mean00/lnPowerSupply/src/rs/ina219/src/lib.rs

#![no_std]
#![allow(dead_code)]

use rust_esprit::rn_i2c::rnI2C;
mod ina219_regs;
pub const INA219_ADDRESS: u8 = 0x40;
use crate::ina219_regs::*;
use rust_esprit::delay_ms;

#[derive(Copy, Clone, PartialEq, PartialOrd)]
pub enum PGA {
    PGA1 = 0,
    PGA2 = 1,
    PGA4 = 2,
    PGA8 = 3,
}

pub struct INA219 {
    i2c: rnI2C,
    address: u8,
    shunt: usize,
    multiplier: f32,
    scale: PGA,
    high_voltage: bool,
    calibration: u16,
}
//-------------------------------------------
fn value_to_volt(value: usize) -> f32 {
    let f = ((value >> 3) * 4) as f32;
    f / 1000.
}

impl INA219 {
    //-------------------------------------------
    pub fn new(
        instance: usize,
        address: u8,
        speed: usize,
        shunt_in_mohm: usize,
        max_current_ampere: usize,
    ) -> Self {
        let multi: f32 = (40. / (shunt_in_mohm as f32)) / 4.096;
        let max_shunt_voltage = shunt_in_mohm * max_current_ampere;
        let divider: PGA;
        const ABS_MAX_SHUNT_VOLTAGE: usize = 330; // in theory the max is 320...
        if max_shunt_voltage > ABS_MAX_SHUNT_VOLTAGE {
            panic!("oops"); // wrong configuration
        } else {
            divider = match max_shunt_voltage {
                160..=ABS_MAX_SHUNT_VOLTAGE => PGA::PGA8,
                80..=159 => PGA::PGA4,
                40..=79 => PGA::PGA2,
                _ => PGA::PGA1,
            };
        }
        //  compute cal
        let mut calf: f32 = 0.04096;
        calf /= (shunt_in_mohm as f32) / 1000.;
        let max_as_float: f32 = max_current_ampere as f32;
        calf /= max_as_float / 32768.; // max 4A
        let cal = (calf + 0.49) as u16;

        let mut r = INA219 {
            i2c: rnI2C::new(instance as u32, speed as u32), // we can create new ones, they are alisased in the C part
            address: address,
            shunt: shunt_in_mohm,
            multiplier: multi,
            scale: divider,
            high_voltage: false,
            calibration: cal,
        };
        r.calibrate(cal);
        r.reconfigure();
        r
    }
    //-------------------------------------------
    pub fn calibrate(&mut self, cal: u16) {
        self.write_register(INA219_REG_CALIBRATION, cal); // 4A max, 20 Ohm
    }
    //-------------------------------------------
    pub fn get_current_scaler(&self) -> PGA {
        return self.scale;
    }
    //-------------------------------------------
    pub fn get_shunt_voltage_raw(&mut self) -> u16 {
        return self.read_register(INA219_REG_SHUNTVOLTAGE);
    }
    //-------------------------------------------
    pub fn get_shunt_voltage_mv(&self) -> isize {
        return 0;
    }
    //-------------------------------------------
    pub fn get_voltage_v(&mut self) -> f32 {
        let mut value = self.get_bus_voltage_raw() as usize;

        let mut flat = value_to_volt(value);
        let mut redo: bool = false;

        if !self.high_voltage && flat > 12.
        // switch to high voltage
        {
            self.high_voltage = true;
            redo = true;
        }
        if !redo && self.high_voltage && flat < 11. {
            self.high_voltage = false;
            redo = true;
        }
        if redo {
            self.reconfigure();
            delay_ms(5);
            value = self.get_bus_voltage_raw() as usize;
            flat = value_to_volt(value);
        }
        flat
    }
    //-------------------------------------------
    pub fn get_current_ma(&mut self) -> usize {
        let current = self.read_register(INA219_REG_CURRENT);
        if (current & (1 << 15)) != 0 {
            return 0; // we dont support negative
        }
        let ma = (current as usize + 5) / 10;
        // round down by 2mA
        if ma > 2 {
            return ma - 2;
        }
        0
    }
    fn inc_scaler(&mut self) {
        self.scale = match self.scale {
            PGA::PGA1 => PGA::PGA2,
            PGA::PGA2 => PGA::PGA4,
            PGA::PGA4 => PGA::PGA8,
            PGA::PGA8 => PGA::PGA8,
        };
    }
    fn dec_scaler(&mut self) {
        self.scale = match self.scale {
            PGA::PGA1 => PGA::PGA1,
            PGA::PGA2 => PGA::PGA1,
            PGA::PGA4 => PGA::PGA2,
            PGA::PGA8 => PGA::PGA4,
        };
    }

    //-------------------------------------------
    fn reconfigure(&mut self) {
        // Set Config register to take into account the settings above
        // 8-> 12 bits, 1 samples average => 0.5 ms to sample
        // 9-> 12 bits, 2 samples average => 1 ms to sample
        // 11-> 12 bits, 32 samples average => 17 ms to sample
        let bit_12_2_samples = 8; // 12 bits, 2 samples average => 1 ms to sample
        let mut config: u16 = match self.high_voltage {
            true => INA219_CONFIG_BVOLTAGERANGE_32V,
            false => 0,
        } + INA219_CONFIG_MODE_SANDBVOLT_CONTINUOUS;

        config |= (self.scale as u16) << 11;
        config |= bit_12_2_samples << 3; // shunt
        config |= bit_12_2_samples << 7; // bus
        self.write_register(INA219_REG_CONFIG, config | INA219_CONFIG_RESET);
        self.write_register(INA219_REG_CALIBRATION, self.calibration);
        self.write_register(INA219_REG_CONFIG, config);
    }
    //-------------------------------------------
    fn write_register(&mut self, reg: u8, value: u16) {
        let datas: [u8; 3] = [reg, (value >> 8) as u8, (value & 0xff) as u8];
        self.i2c.write_to(self.address, &datas);
    }
    //-------------------------------------------
    fn read_register(&mut self, reg: u8) -> u16 {
        let mut datas: [u8; 2] = [0, 0];
        let regs: [u8; 1] = [reg];
        self.i2c.write_to(self.address, &regs);
        self.i2c.read_from(self.address, &mut datas);
        let v = (((datas[0] as u16) << 8) as u16) + (datas[1] as u16);
        v
    }
    //-------------------------------------------
    fn get_bus_voltage_raw(&mut self) -> u16 {
        self.read_register(INA219_REG_BUSVOLTAGE)
    }
    //-------------------------------------------
    fn set_scaler(&mut self, scale: PGA) {
        self.scale = scale;
    }
    pub fn test_raw(&mut self, scale: PGA) -> u16 {
        self.set_scaler(scale);
        self.reconfigure();
        return self.get_shunt_voltage_raw();
    }
}
